toms74209200/CO2MO/learning/chapt2/co2_sensor/mhz19b_uart.cpp

/**
 * @file mhz19b_uart.cpp
 * @brief MH-Z19B CO2 sensor read
 * 
 * Copyright (c) 2021 toms74209200
 * This software is released under the MIT License.
 * http://opensource.org/licenses/mit-license.php
 */

#include "mhz19b_uart.h"

const byte START_BYTE = 0xFF;
const byte REQUEST_SENSOR = 0x01;
const byte READ_CO2 = 0x86;
const byte CHECK_SUM = 0x79;

/**
 * @brief Initializes serial port
 */
void init_co2(byte rx, byte tx) {
  Serial1.setRX(rx);
  Serial1.setTX(tx);
  Serial1.begin(9600);
}

/**
 * @brief Reads MH-Z19B
 * @param[out] pointer of response data
 * @return bool result of successful reading
 */
bool read_mhz19b(byte* response) {
  byte cmd[9] = {START_BYTE,REQUEST_SENSOR,READ_CO2,0x00,0x00,0x00,0x00,0x00,CHECK_SUM};
  Serial1.write(cmd, 9);
  
  const uint16_t retry_count = 10;
  for (uint16_t i = 1; ; i++) {
    byte buf[2];
    Serial1.readBytes(buf, sizeof(buf));
    if (buf[0] == 0xFF && buf[1] == 0x86) {
      break;
    }
    if (i > retry_count) {
      return false;
    }
  }
  byte buf[7];
  Serial1.readBytes(buf, sizeof(buf));
  memcpy(response, buf, sizeof(response));
  return true;

}
/**
 * @brief Gets CO2 data
 * @return int CO2 data
 */
uint16_t get_co2() {
  byte response[7];

  if (!read_mhz19b(response)) {
    return 0;
  }

  byte responseHigh = (byte) response[0];
  byte responseLow = (byte) response[1];
  uint16_t co2_data = (responseHigh << 8) + responseLow;
  return co2_data;
}

/**
 * @brief Get temperature data
 * @return int temperature data
 */
int16_t get_temperature() {
  byte response[7];

  if (!read_mhz19b(response)) {
    return 0;
  }

  int16_t temperature = response[2] - 40;

  return temperature;
}
